PA3EFR/FH2_repeater/Arduino Nano - 991/WhatsApp Image 2026-05-23 at 14.03.42 (2).jpeg

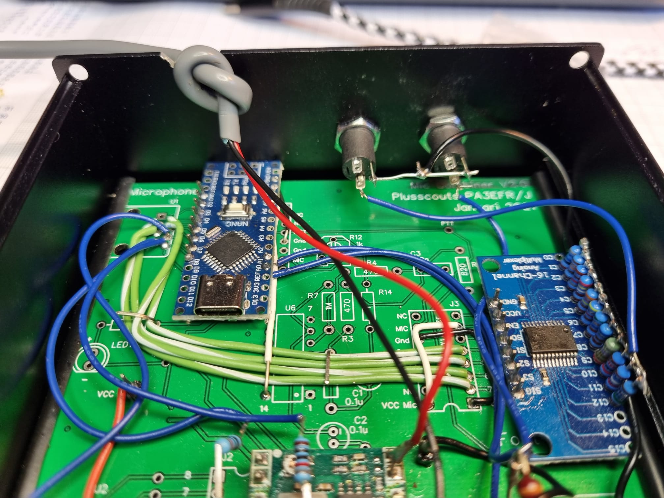
Arduino Nano - 991/WhatsApp Image 2026-05-23 at 14.03.42 (2).jpeg
