PA3EFR/FH2_repeater/Arduino Nano - 991/WhatsApp Image 2026-06-02 at 10.33.46 (2).jpeg

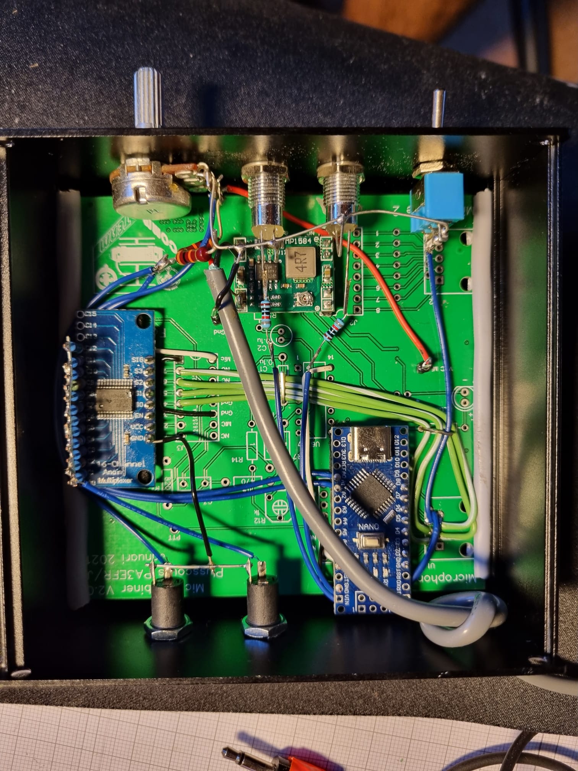
Arduino Nano - 991/WhatsApp Image 2026-06-02 at 10.33.46 (2).jpeg
